JohnInTheGarage/Moonlyte/circuit/focuser/focuser.kicad_pcb

## KiCad design advanced-alu/schematics/advanced-alu/comparison-test-unit.kicad_sch

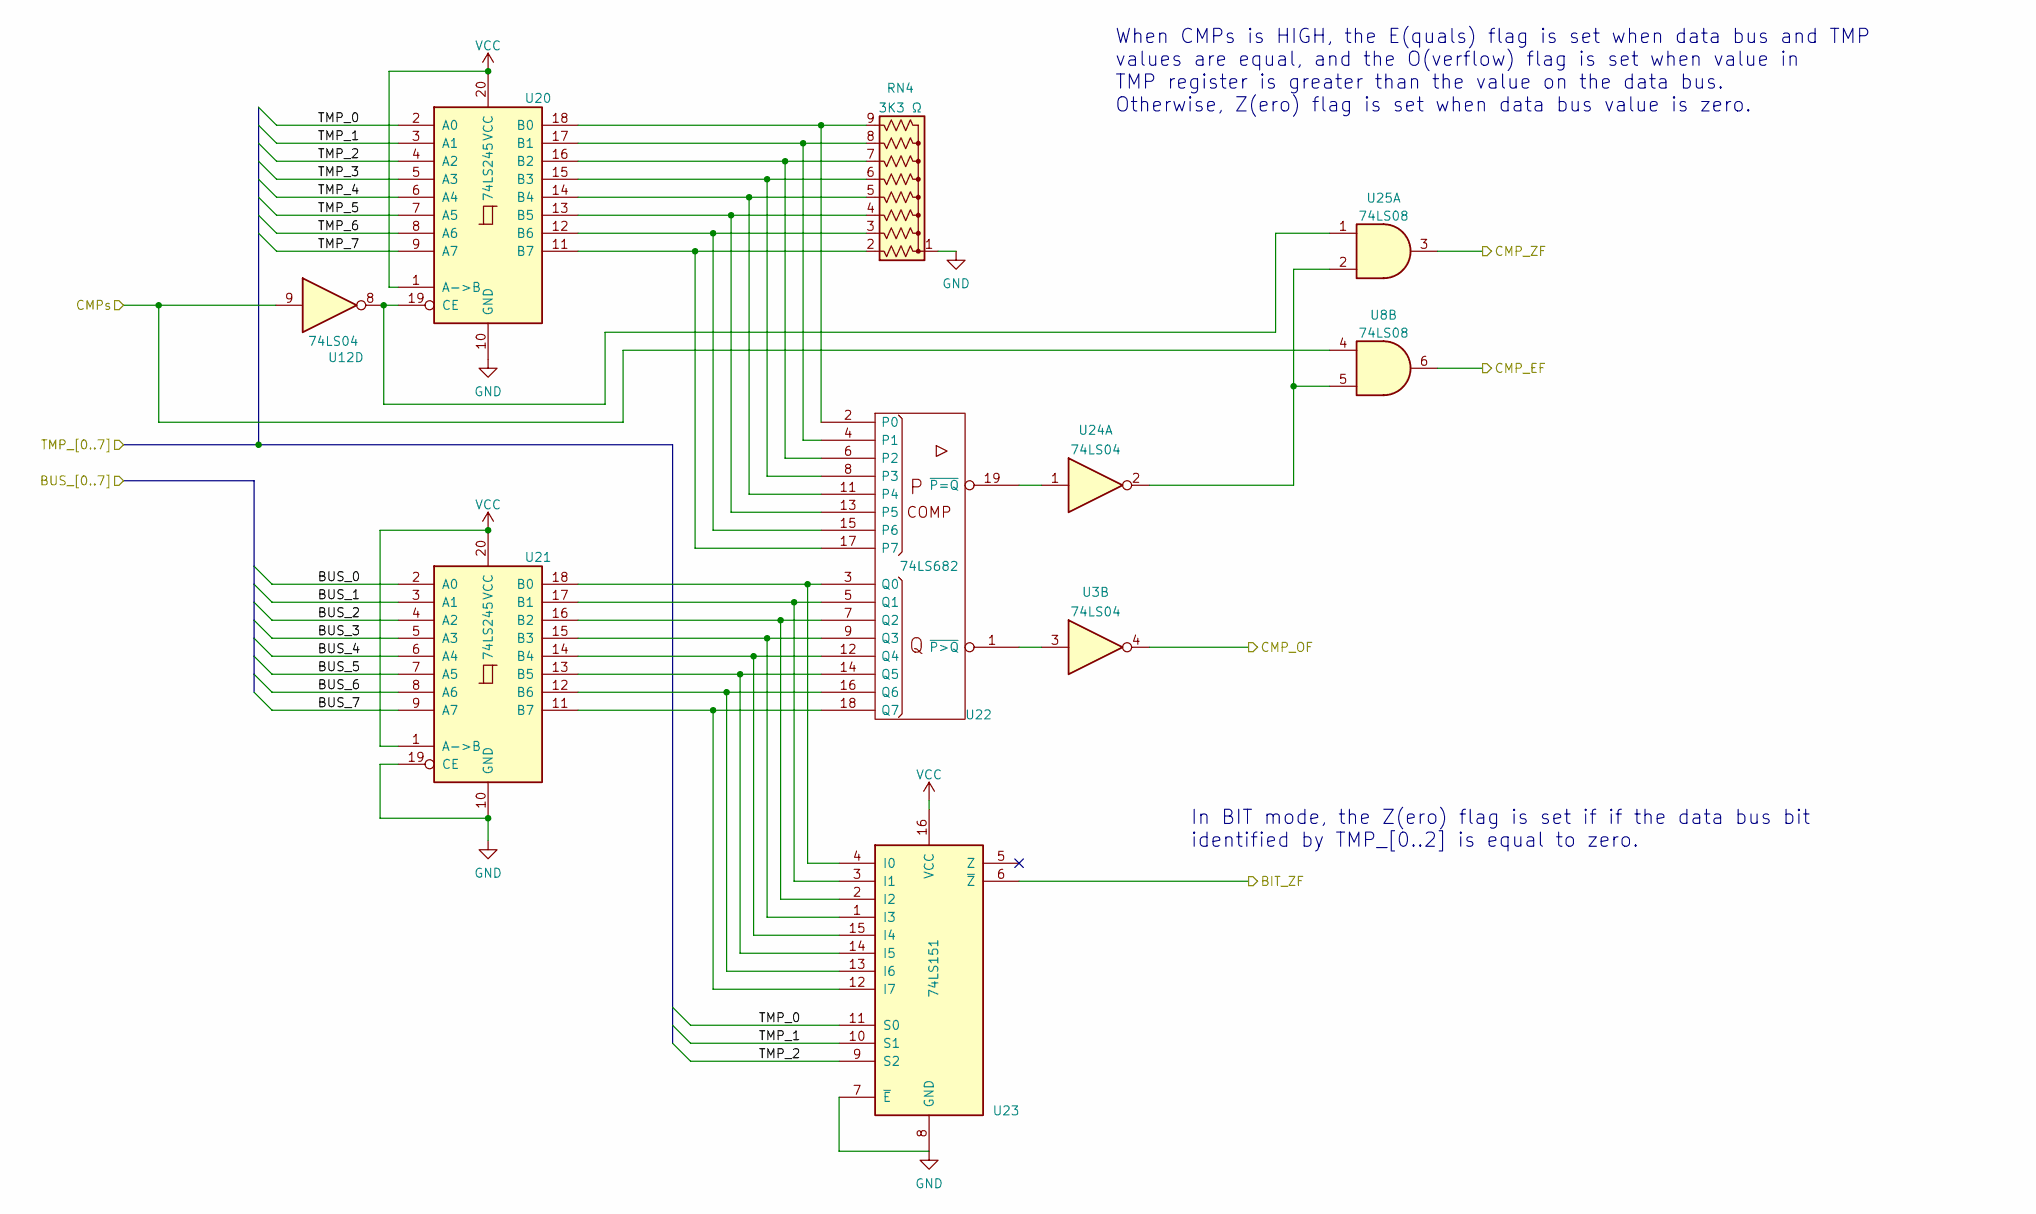
[picture p20: schematic comparison-test-unit.kicad_sch]

Parts:
RN4: 3K3 Ω; R_Array_SIP9
U3, U12, U24: 74LS04
U8, U25: 74LS08
U20, U21: 74LS245
U22: 74LS682
U23: 74LS151

Connections:
BIT_ZF: U23.6 (~Z)
BUS_0: U21.2 (A0)
BUS_1: U21.3 (A1)
BUS_2: U21.4 (A2)
BUS_3: U21.5 (A3)
BUS_4: U21.6 (A4)
BUS_5: U21.7 (A5)
BUS_6: U21.8 (A6)
BUS_7: U21.9 (A7)
CMP_EF: U8.6
CMP_OF: U3.4
CMP_ZF: U25.3
CMPs: U8.4, U12.9
GND: RN4.1 (common), U20.10 (GND), U21.10 (GND), U21.19 (CE), U23.7 (~E), U23.8 (GND)
unnamed: RN4.2 (R1), U20.11 (B7), U22.17 (P7)
unnamed: RN4.3 (R2), U20.12 (B6), U22.15 (P6)
unnamed: RN4.4 (R3), U20.13 (B5), U22.13 (P5)
unnamed: RN4.5 (R4), U20.14 (B4), U22.11 (P4)
unnamed: RN4.6 (R5), U20.15 (B3), U22.8 (P3)
unnamed: RN4.7 (R6), U20.16 (B2), U22.6 (P2)
unnamed: RN4.8 (R7), U20.17 (B1), U22.4 (P1)
unnamed: RN4.9 (R8), U20.18 (B0), U22.2 (P0)
unnamed: U12.8, U20.19 (CE), U25.1
unnamed: U21.11 (B7), U22.18 (Q7), U23.12 (I7)
unnamed: U21.12 (B6), U22.16 (Q6), U23.13 (I6)
unnamed: U21.13 (B5), U22.14 (Q5), U23.14 (I5)
unnamed: U21.14 (B4), U22.12 (Q4), U23.15 (I4)
unnamed: U21.15 (B3), U22.9 (Q3), U23.1 (I3)
unnamed: U21.16 (B2), U22.7 (Q2), U23.2 (I2)
unnamed: U21.17 (B1), U22.5 (Q1), U23.3 (I1)
unnamed: U21.18 (B0), U22.3 (Q0), U23.4 (I0)
unnamed: U3.3, U22.1 (~P>Q)
unnamed: U22.19 (~P=Q), U24.1
unnamed: U8.5, U24.2, U25.2
TMP_0: U20.2 (A0), U23.11 (S0)
TMP_1: U20.3 (A1), U23.10 (S1)
TMP_2: U20.4 (A2), U23.9 (S2)
TMP_3: U20.5 (A3)
TMP_4: U20.6 (A4)
TMP_5: U20.7 (A5)
TMP_6: U20.8 (A6)
TMP_7: U20.9 (A7)
VCC: U20.1 (A->B), U20.20 (VCC), U21.1 (A->B), U21.20 (VCC), U23.16 (VCC)

Notes on the sheet:
In BIT mode, the Z(ero) flag is set if if the data bus bit identified by TMP_[0..2] is equal to zero.
When CMPs is HIGH, the E(quals) flag is set when data bus and TMP values are equal, and the O(verflow) flag is set when value in TMP register is greater than the value on the data bus. Otherwise, Z(ero) flag is set when data bus value is zero.
