JohnInTheGarage/Moonlyte/circuit/focuser/focuser.kicad_pcb

## KiCad design advanced-alu/schematics/advanced-alu/flags-register.kicad_sch

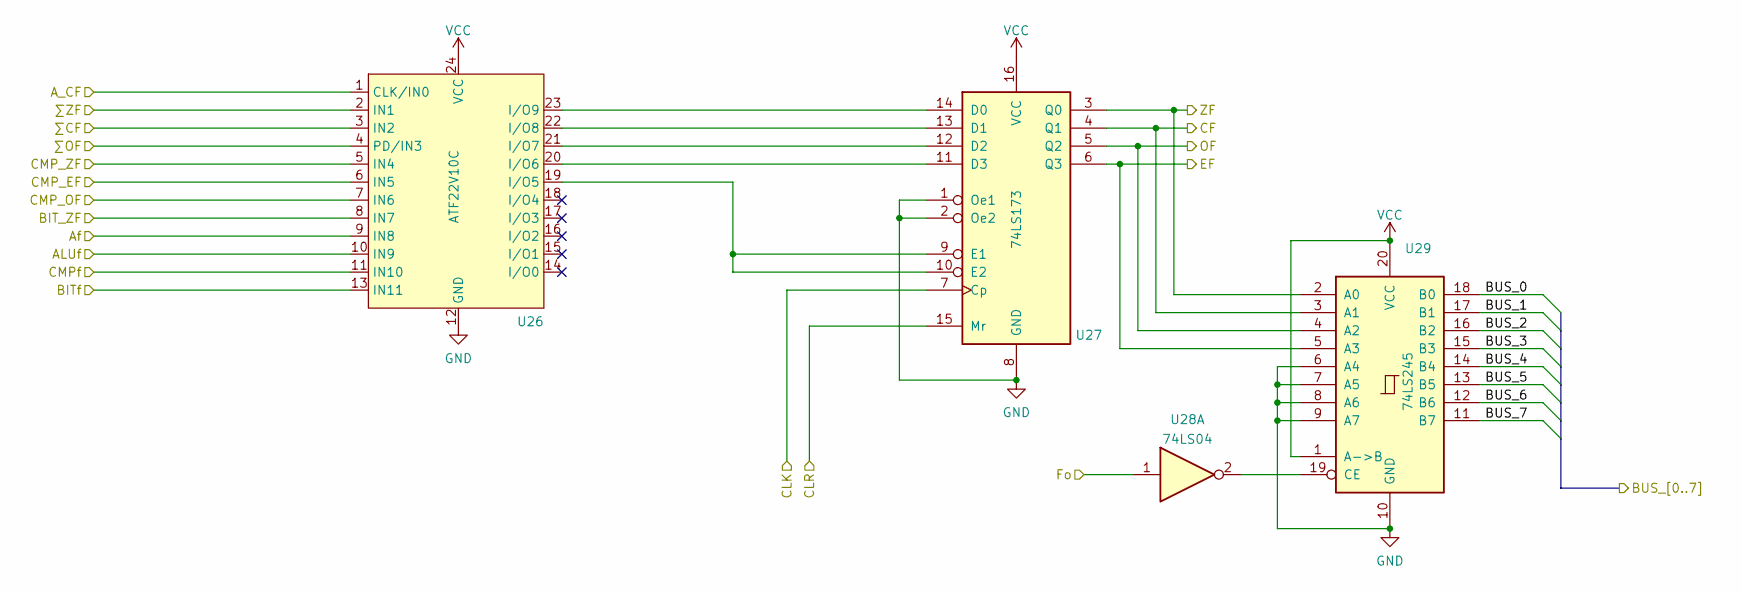
[picture p21: schematic flags-register.kicad_sch]

Parts:
U26: ATF22V10C
U27: 74LS173
U28: 74LS04
U29: 74LS245

Connections:
ALUf: U26.10 (IN9)
A_CF: U26.1 (CLK/IN0)
Af: U26.9 (IN8)
BIT_ZF: U26.8 (IN7)
BITf: U26.13 (IN11)
BUS_0: U29.18 (B0)
BUS_1: U29.17 (B1)
BUS_2: U29.16 (B2)
BUS_3: U29.15 (B3)
BUS_4: U29.14 (B4)
BUS_5: U29.13 (B5)
BUS_6: U29.12 (B6)
BUS_7: U29.11 (B7)
CF: U27.4 (Q1), U29.3 (A1)
CLK: U27.7 (Cp)
CLR: U27.15 (Mr)
CMP_EF: U26.6 (IN5)
CMP_OF: U26.7 (IN6)
CMP_ZF: U26.5 (IN4)
CMPf: U26.11 (IN10)
EF: U27.6 (Q3), U29.5 (A3)
Fo: U28.1
GND: U26.12 (GND), U27.1 (Oe1), U27.2 (Oe2), U27.8 (GND), U29.6 (A4), U29.7 (A5), U29.8 (A6), U29.9 (A7), U29.10 (GND)
unnamed: U26.19 (I/O5), U27.9 (E1), U27.10 (E2)
unnamed: U26.20 (I/O6), U27.11 (D3)
unnamed: U26.21 (I/O7), U27.12 (D2)
unnamed: U26.22 (I/O8), U27.13 (D1)
unnamed: U26.23 (I/O9), U27.14 (D0)
unnamed: U28.2, U29.19 (CE)
OF: U27.5 (Q2), U29.4 (A2)
VCC: U26.24 (VCC), U27.16 (VCC), U29.1 (A->B), U29.20 (VCC)
ZF: U27.3 (Q0), U29.2 (A0)
∑CF: U26.3 (IN2)
∑OF: U26.4 (PD/IN3)
∑ZF: U26.2 (IN1)
