JohnInTheGarage/Moonlyte/circuit/focuser/focuser.kicad_pcb

## KiCad design advanced-alu/schematics/control-logic/control-logic.kicad_sch

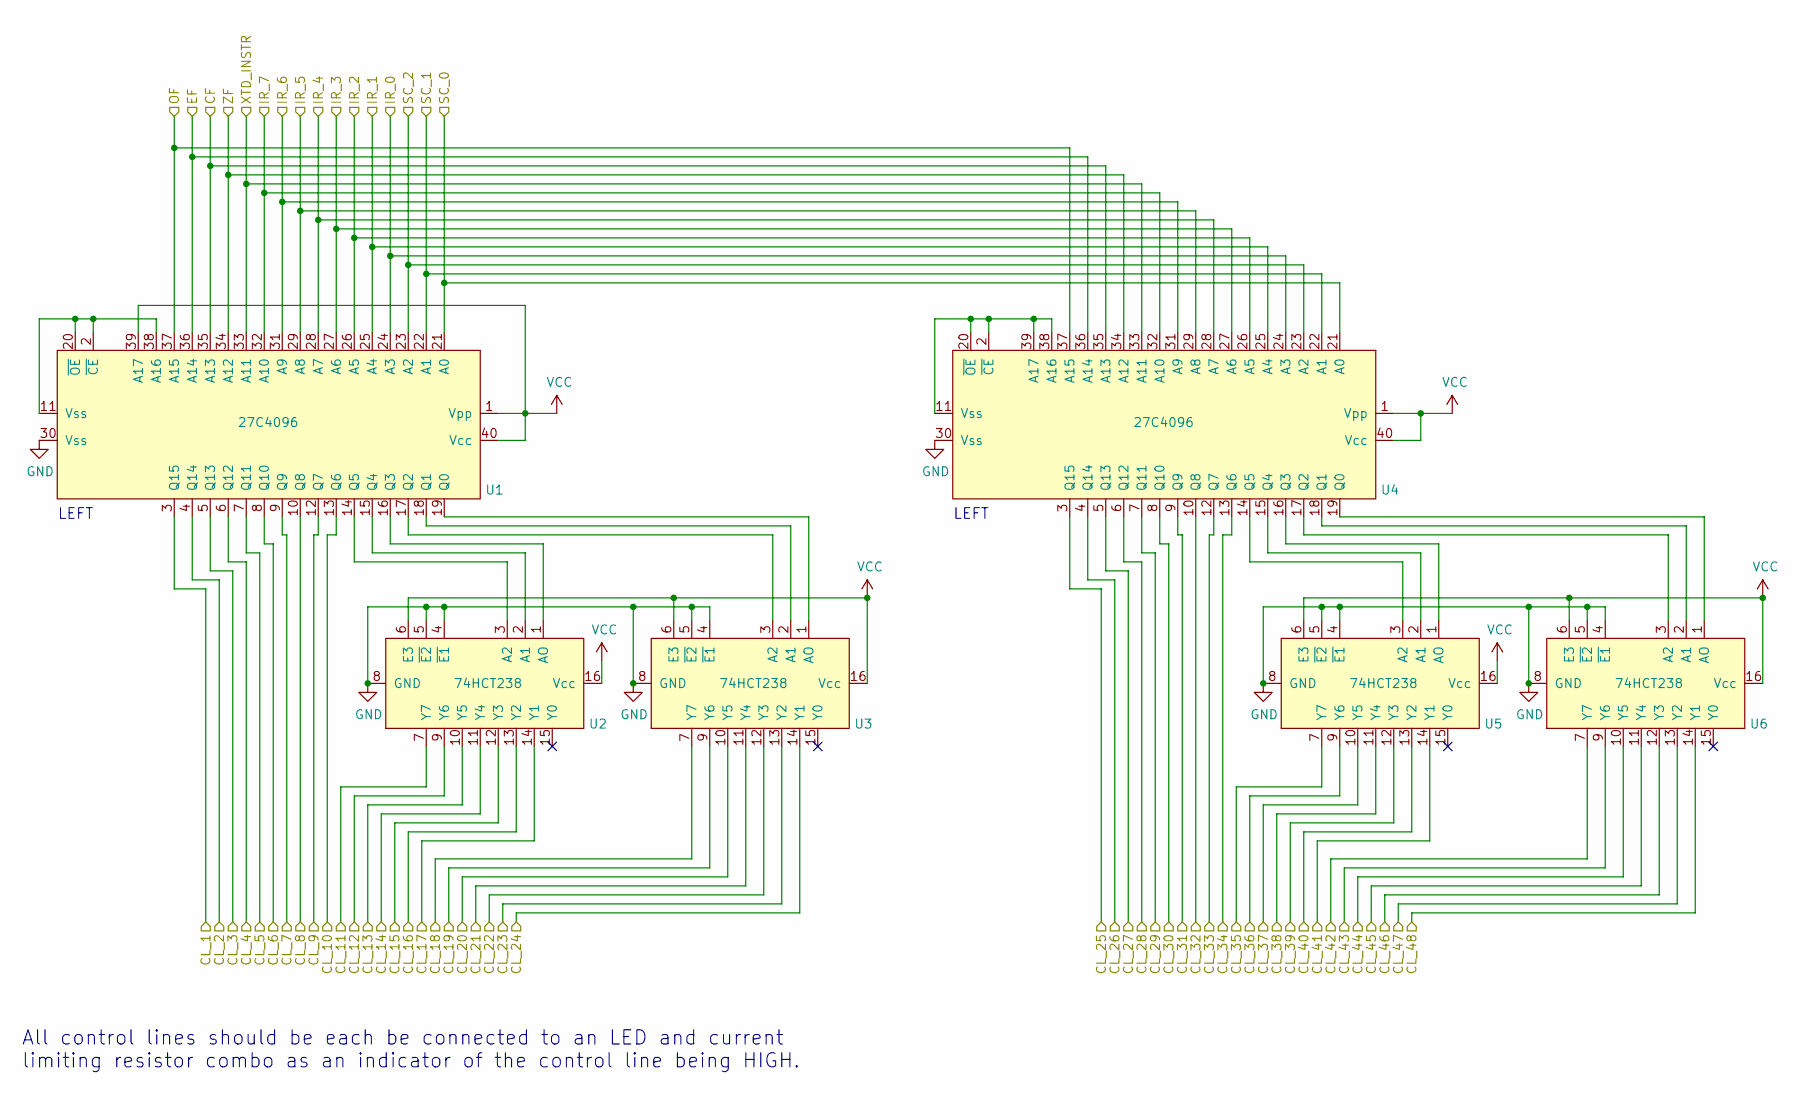
[picture p23: schematic control-logic.kicad_sch]

Parts:
U1, U4: 27C4096
U2, U3, U5, U6: 74HCT238

Connections:
CF: U1.35 (A13), U4.35 (A13)
CL_1: U1.3 (Q15)
CL_2: U1.4 (Q14)
CL_3: U1.5 (Q13)
CL_4: U1.6 (Q12)
CL_5: U1.7 (Q11)
CL_6: U1.8 (Q10)
CL_7: U1.9 (Q9)
CL_8: U1.10 (Q8)
CL_9: U1.12 (Q7)
CL_10: U1.13 (Q6)
CL_11: U2.7 (Y7)
CL_12: U2.9 (Y6)
CL_13: U2.10 (Y5)
CL_14: U2.11 (Y4)
CL_15: U2.12 (Y3)
CL_16: U2.13 (Y2)
CL_17: U2.14 (Y1)
CL_18: U3.7 (Y7)
CL_19: U3.9 (Y6)
CL_20: U3.10 (Y5)
CL_21: U3.11 (Y4)
CL_22: U3.12 (Y3)
CL_23: U3.13 (Y2)
CL_24: U3.14 (Y1)
CL_25: U4.3 (Q15)
CL_26: U4.4 (Q14)
CL_27: U4.5 (Q13)
CL_28: U4.6 (Q12)
CL_29: U4.7 (Q11)
CL_30: U4.8 (Q10)
CL_31: U4.9 (Q9)
CL_32: U4.10 (Q8)
CL_33: U4.12 (Q7)
CL_34: U4.13 (Q6)
CL_35: U5.7 (Y7)
CL_36: U5.9 (Y6)
CL_37: U5.10 (Y5)
CL_38: U5.11 (Y4)
CL_39: U5.12 (Y3)
CL_40: U5.13 (Y2)
CL_41: U5.14 (Y1)
CL_42: U6.7 (Y7)
CL_43: U6.9 (Y6)
CL_44: U6.10 (Y5)
CL_45: U6.11 (Y4)
CL_46: U6.12 (Y3)
CL_47: U6.13 (Y2)
CL_48: U6.14 (Y1)
EF: U1.36 (A14), U4.36 (A14)
GND: U1.30 (Vss), U2.4 (~E1), U2.5 (~E2), U2.8 (GND), U3.4 (~E1), U3.5 (~E2), U3.8 (GND), U4.30 (Vss), U5.4 (~E1), U5.5 (~E2), U5.8 (GND), U6.4 (~E1), U6.5 (~E2), U6.8 (GND)
IR_0: U1.24 (A3), U4.24 (A3)
IR_1: U1.25 (A4), U4.25 (A4)
IR_2: U1.26 (A5), U4.26 (A5)
IR_3: U1.27 (A6), U4.27 (A6)
IR_4: U1.28 (A7), U4.28 (A7)
IR_5: U1.29 (A8), U4.29 (A8)
IR_6: U1.31 (A9), U4.31 (A9)
IR_7: U1.32 (A10), U4.32 (A10)
unnamed: U1.2 (~CE), U1.11 (Vss), U1.20 (~OE), U1.38 (A16)
unnamed: U1.14 (Q5), U2.3 (A2)
unnamed: U1.15 (Q4), U2.2 (A1)
unnamed: U1.16 (Q3), U2.1 (AO)
unnamed: U1.17 (Q2), U3.3 (A2)
unnamed: U1.18 (Q1), U3.2 (A1)
unnamed: U1.19 (Q0), U3.1 (AO)
unnamed: U4.2 (~CE), U4.11 (Vss), U4.20 (~OE), U4.38 (A16), U4.39 (A17)
unnamed: U4.14 (Q5), U5.3 (A2)
unnamed: U4.15 (Q4), U5.2 (A1)
unnamed: U4.16 (Q3), U5.1 (AO)
unnamed: U4.17 (Q2), U6.3 (A2)
unnamed: U4.18 (Q1), U6.2 (A1)
unnamed: U4.19 (Q0), U6.1 (AO)
OF: U1.37 (A15), U4.37 (A15)
SC_0: U1.21 (A0), U4.21 (A0)
SC_1: U1.22 (A1), U4.22 (A1)
SC_2: U1.23 (A2), U4.23 (A2)
VCC: U1.1 (Vpp), U1.39 (A17), U1.40 (Vcc), U2.6 (E3), U2.16 (Vcc), U3.6 (E3), U3.16 (Vcc), U4.1 (Vpp), U4.40 (Vcc), U5.6 (E3), U5.16 (Vcc), U6.6 (E3), U6.16 (Vcc)
XTD_INSTR: U1.33 (A11), U4.33 (A11)
ZF: U1.34 (A12), U4.34 (A12)

Notes on the sheet:
All control lines should be each be connected to an LED and current limiting resistor combo as an indicator of the control line being HIGH.
LEFT
