JohnInTheGarage/Moonlyte/circuit/focuser/focuser.kicad_pcb

## KiCad design increment-registers/schematics/alu/alu.sch

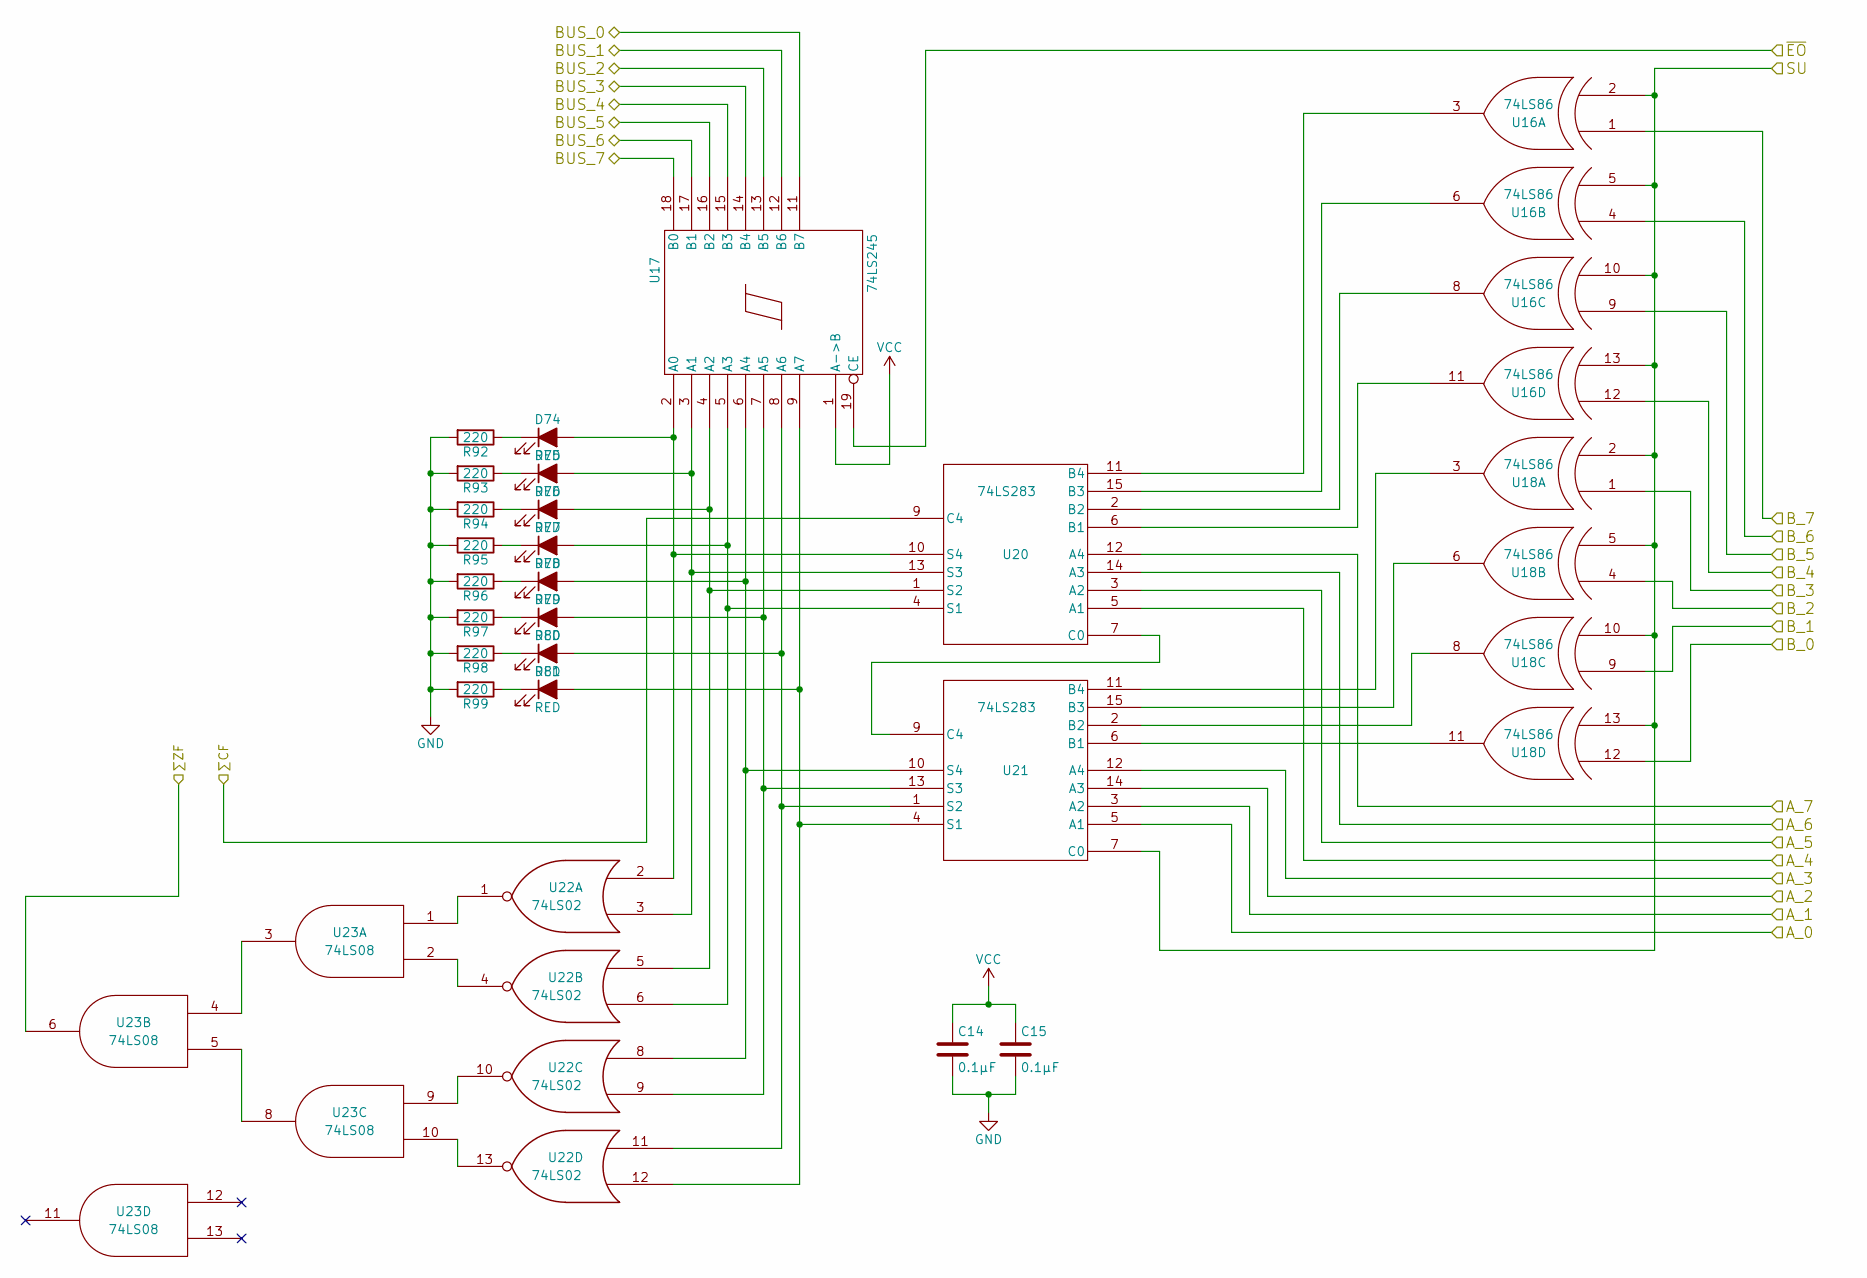
[picture p26: schematic alu.sch]

Parts:
C14, C15: 0.1µF; C_Disc_D4.3mm_W1.9mm_P5.00mm
D74, D75, D76, D77, D78, D79, D80, D81: RED; LED_D5.0mm
R92, R93, R94, R95, R96, R97, R98, R99: 220; R_Axial_DIN0207_L6.3mm_D2.5mm_P7.62mm_Horizontal
U16, U18: 74LS86; DIP-14_W7.62mm
U17: 74LS245; DIP-20_W7.62mm
U20, U21: 74LS283; DIP-16_W7.62mm
U22: 74LS02; DIP-14_W7.62mm
U23: 74LS08; DIP-14_W7.62mm

Connections:
A_0: U21.5 (A1)
A_1: U21.3 (A2)
A_2: U21.14 (A3)
A_3: U21.12 (A4)
A_4: U20.5 (A1)
A_5: U20.3 (A2)
A_6: U20.14 (A3)
A_7: U20.12 (A4)
BUS_0: U17.11 (B7)
BUS_1: U17.12 (B6)
BUS_2: U17.13 (B5)
BUS_3: U17.14 (B4)
BUS_4: U17.15 (B3)
BUS_5: U17.16 (B2)
BUS_6: U17.17 (B1)
BUS_7: U17.18 (B0)
B_0: U18.12 (IN1)
B_1: U18.9 (IN1)
B_2: U18.4 (IN1)
B_3: U18.1 (IN1)
B_4: U16.12 (IN1)
B_5: U16.9 (IN1)
B_6: U16.4 (IN1)
B_7: U16.1 (IN1)
GND: C14.2, C15.2, R92.2, R93.2, R94.2, R95.2, R96.2, R97.2, R98.2, R99.2
unnamed: D74.1 (K), R92.1
unnamed: D74.2 (A), U17.2 (A0), U20.10 (S4), U22.2
unnamed: D75.1 (K), R93.1
unnamed: D75.2 (A), U17.3 (A1), U20.13 (S3), U22.3
unnamed: D76.1 (K), R94.1
unnamed: D76.2 (A), U17.4 (A2), U20.1 (S2), U22.5
unnamed: D77.1 (K), R95.1
unnamed: D77.2 (A), U17.5 (A3), U20.4 (S1), U22.6
unnamed: D78.1 (K), R96.1
unnamed: D78.2 (A), U17.6 (A4), U21.10 (S4), U22.8
unnamed: D79.1 (K), R97.1
unnamed: D79.2 (A), U17.7 (A5), U21.13 (S3), U22.9
unnamed: D80.1 (K), R98.1
unnamed: D80.2 (A), U17.8 (A6), U21.1 (S2), U22.11
unnamed: D81.1 (K), R99.1
unnamed: D81.2 (A), U17.9 (A7), U21.4 (S1), U22.12
unnamed: U16.3 (OUT), U20.11 (B4)
unnamed: U16.6 (OUT), U20.15 (B3)
unnamed: U16.8 (OUT), U20.2 (B2)
unnamed: U16.11 (OUT), U20.6 (B1)
unnamed: U18.3 (OUT), U21.11 (B4)
unnamed: U18.6 (OUT), U21.15 (B3)
unnamed: U18.8 (OUT), U21.2 (B2)
unnamed: U18.11 (OUT), U21.6 (B1)
unnamed: U20.7 (C0), U21.9 (C4)
unnamed: U22.1, U23.1
unnamed: U22.4, U23.2
unnamed: U22.10, U23.9
unnamed: U22.13, U23.10
unnamed: U23.3, U23.4
unnamed: U23.5, U23.8
SU: U16.2 (IN2), U16.5 (IN2), U16.10 (IN2), U16.13 (IN2), U18.2 (IN2), U18.5 (IN2), U18.10 (IN2), U18.13 (IN2), U21.7 (C0)
VCC: C14.1, C15.1, U17.1 (A->B)
~EO: U17.19 (CE)
∑CF: U20.9 (C4)
∑ZF: U23.6
