JohnInTheGarage/Moonlyte/circuit/focuser/focuser.kicad_pcb

## KiCad design increment-registers/schematics/counting-register/counting-register.kicad_sch

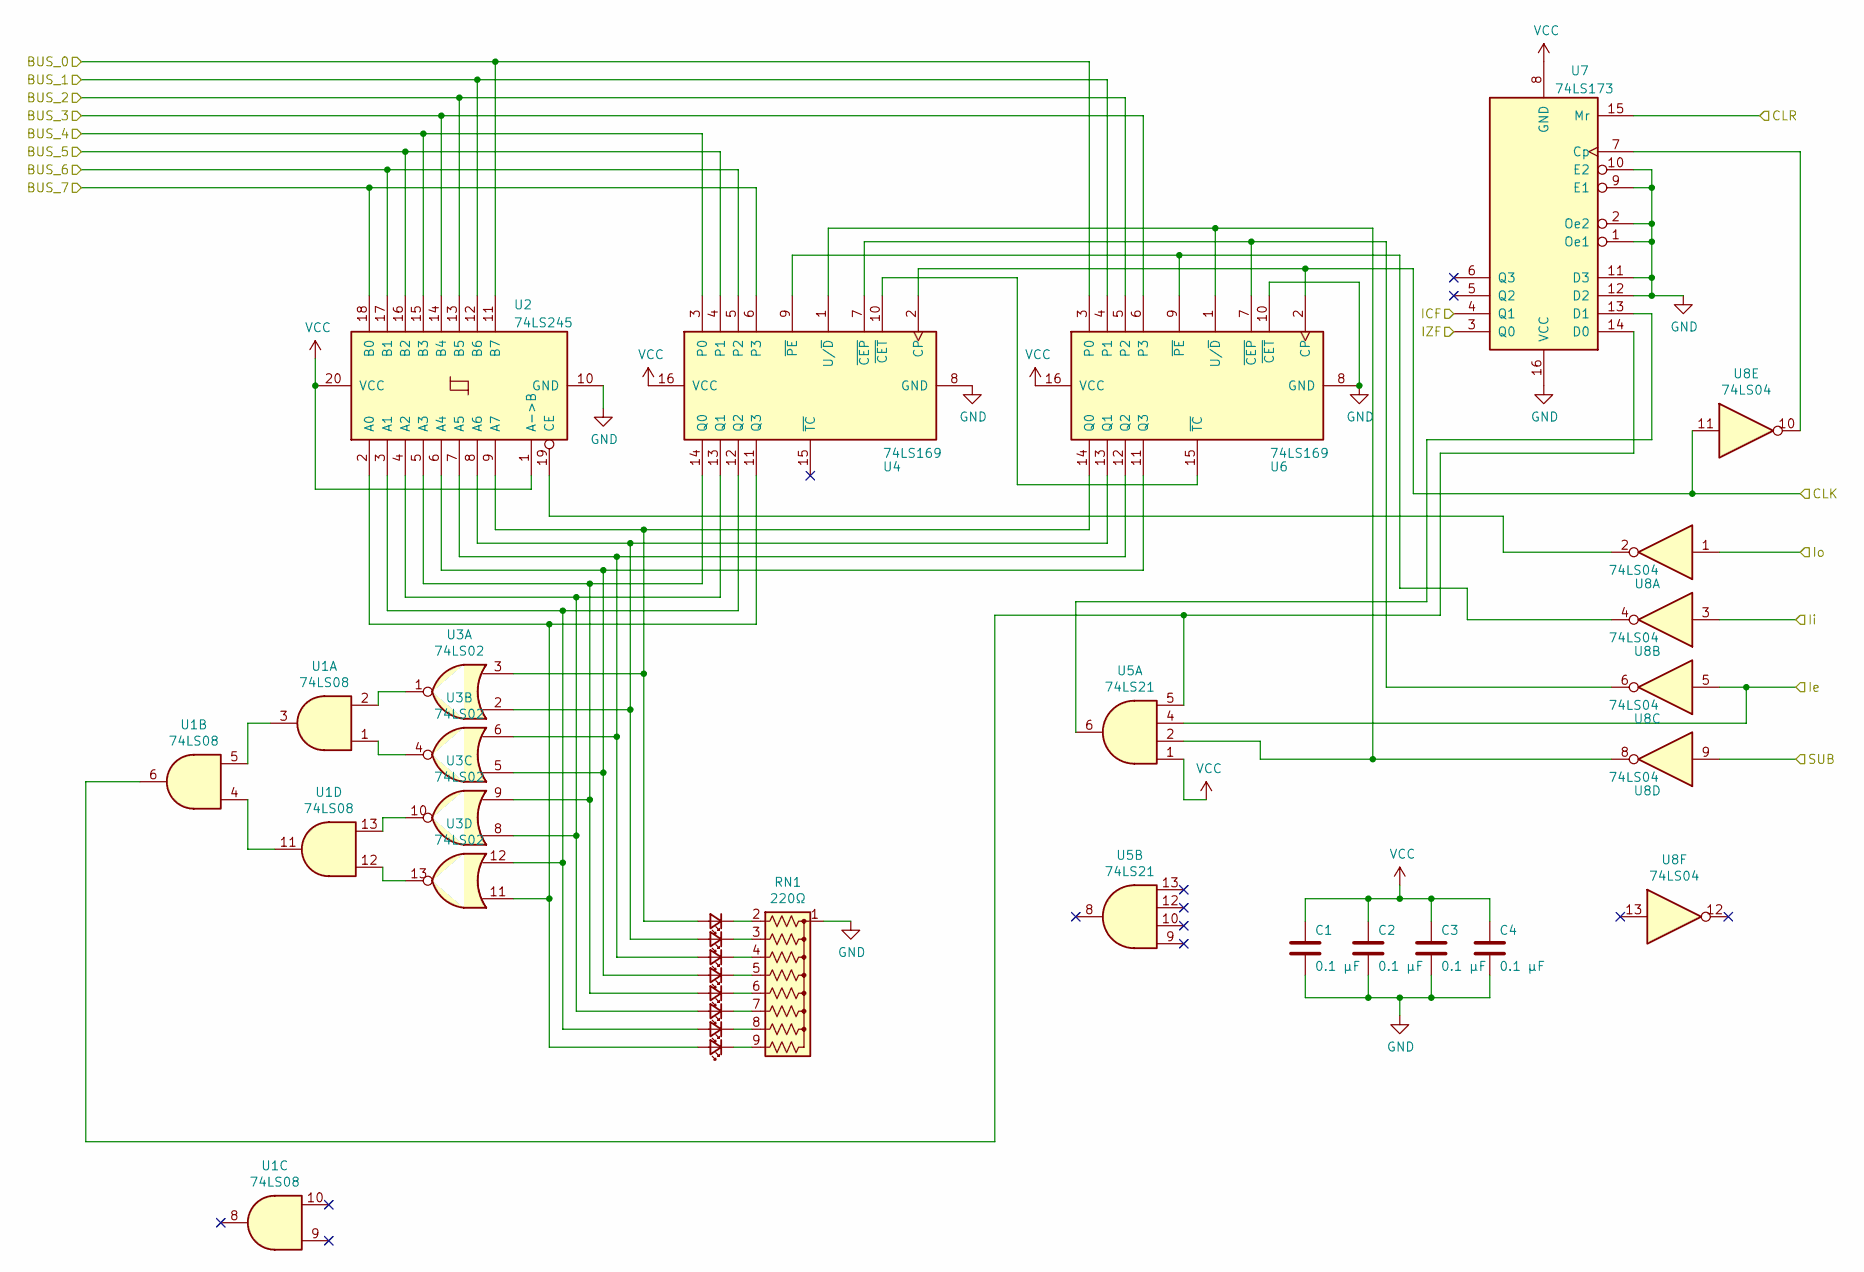
[picture p27: schematic counting-register.kicad_sch]

Parts:
C1, C2, C3, C4: 0.1 µF
D1, D2, D3, D4, D5, D6, D7, D8: LED_Small
RN1: 220Ω; R_Array_SIP9
U1: 74LS08
U2: 74LS245
U3: 74LS02
U4, U6: 74LS169
U5: 74LS21
U7: 74LS173
U8: 74LS04

Connections:
BUS_0: U2.11 (B7), U6.3 (P0)
BUS_1: U2.12 (B6), U6.4 (P1)
BUS_2: U2.13 (B5), U6.5 (P2)
BUS_3: U2.14 (B4), U6.6 (P3)
BUS_4: U2.15 (B3), U4.3 (P0)
BUS_5: U2.16 (B2), U4.4 (P1)
BUS_6: U2.17 (B1), U4.5 (P2)
BUS_7: U2.18 (B0), U4.6 (P3)
CLK: U4.2 (CP), U6.2 (CP), U8.11
CLR: U7.15 (Mr)
GND: C1.2, C2.2, C3.2, C4.2, RN1.1 (common), U2.10 (GND), U4.8 (GND), U6.8 (GND), U6.10 (~CET), U7.1 (Oe1), U7.2 (Oe2), U7.9 (E1), U7.10 (E2), U7.11 (D3), U7.12 (D2), U7.16 (VCC)
ICF: U7.4 (Q1)
IZF: U7.3 (Q0)
Ie: U5.4, U8.5
Ii: U8.3
Io: U8.1
unnamed: D1.1 (K), RN1.2 (R1)
unnamed: D1.2 (A), U2.9 (A7), U3.3, U6.14 (Q0)
unnamed: D2.1 (K), RN1.3 (R2)
unnamed: D2.2 (A), U2.8 (A6), U3.2, U6.13 (Q1)
unnamed: D3.1 (K), RN1.4 (R3)
unnamed: D3.2 (A), U2.7 (A5), U3.6, U6.12 (Q2)
unnamed: D4.1 (K), RN1.5 (R4)
unnamed: D4.2 (A), U2.6 (A4), U3.5, U6.11 (Q3)
unnamed: D5.1 (K), RN1.6 (R5)
unnamed: D5.2 (A), U2.5 (A3), U3.9, U4.14 (Q0)
unnamed: D6.1 (K), RN1.7 (R6)
unnamed: D6.2 (A), U2.4 (A2), U3.8, U4.13 (Q1)
unnamed: D7.1 (K), RN1.8 (R7)
unnamed: D7.2 (A), U2.3 (A1), U3.12, U4.12 (Q2)
unnamed: D8.1 (K), RN1.9 (R8)
unnamed: D8.2 (A), U2.2 (A0), U3.11, U4.11 (Q3)
unnamed: U1.1, U3.4
unnamed: U1.2, U3.1
unnamed: U1.3, U1.5
unnamed: U1.6, U5.5, U7.14 (D0)
unnamed: U1.4, U1.11
unnamed: U1.12, U3.13
unnamed: U1.13, U3.10
unnamed: U2.19 (CE), U8.2
unnamed: U4.1 (U/~D), U5.2, U6.1 (U/~D), U8.8
unnamed: U4.7 (~CEP), U6.7 (~CEP), U8.6
unnamed: U4.9 (~PE), U6.9 (~PE), U8.4
unnamed: U4.10 (~CET), U6.15 (~TC)
unnamed: U5.6, U7.13 (D1)
unnamed: U7.7 (Cp), U8.10
SUB: U8.9
VCC: C1.1, C2.1, C3.1, C4.1, U2.1 (A->B), U2.20 (VCC), U4.16 (VCC), U5.1, U6.16 (VCC), U7.8 (GND)
