JohnInTheGarage/Moonlyte/circuit/focuser/focuser.kicad_pcb

## KiCad design lcd-display/schematics/lcd-display/lcd-display.kicad_sch

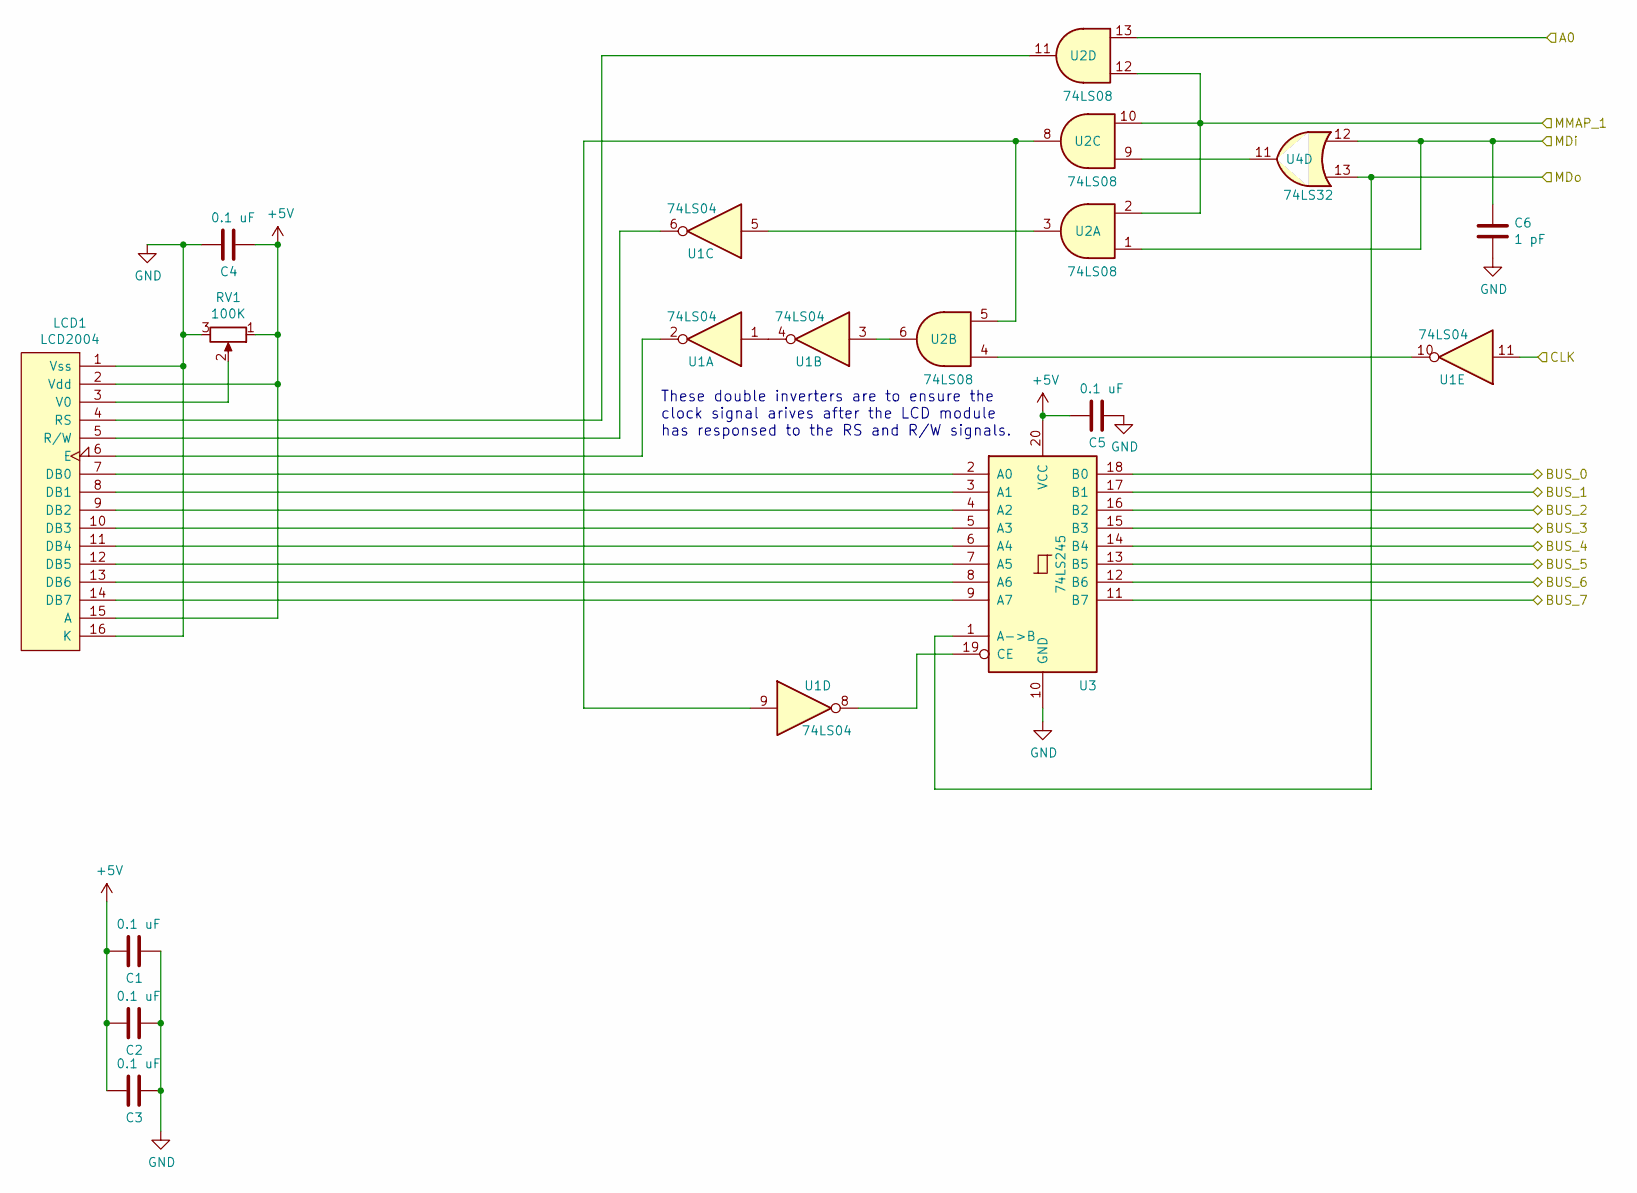
[picture p32: schematic lcd-display.kicad_sch]

Parts:
C1, C2, C3, C4, C5: 0.1 uF
C6: 1 pF
LCD1: LCD2004
RV1: 100K
U1: 74LS04
U2: 74LS08
U3: 74LS245
U4: 74LS32

Connections:
+5V: C1.2, C2.2, C3.2, C4.1, C5.2, LCD1.2 (Vdd), LCD1.15 (A), RV1.1, U3.20 (VCC)
A0: U2.13
BUS_0: U3.18 (B0)
BUS_1: U3.17 (B1)
BUS_2: U3.16 (B2)
BUS_3: U3.15 (B3)
BUS_4: U3.14 (B4)
BUS_5: U3.13 (B5)
BUS_6: U3.12 (B6)
BUS_7: U3.11 (B7)
CLK: U1.11
GND: C1.1, C2.1, C3.1, C4.2, C5.1, C6.2, LCD1.1 (Vss), LCD1.16 (K), RV1.3, U3.10 (GND)
MDi: C6.1, U2.1, U4.12
MDo: U3.1 (A->B), U4.13
MMAP_1: U2.2, U2.10, U2.12
unnamed: LCD1.3 (V0), RV1.2
unnamed: LCD1.4 (RS), U2.11
unnamed: LCD1.5 (R/W), U1.6
unnamed: LCD1.6 (E), U1.2
unnamed: LCD1.7 (DB0), U3.2 (A0)
unnamed: LCD1.8 (DB1), U3.3 (A1)
unnamed: LCD1.9 (DB2), U3.4 (A2)
unnamed: LCD1.10 (DB3), U3.5 (A3)
unnamed: LCD1.11 (DB4), U3.6 (A4)
unnamed: LCD1.12 (DB5), U3.7 (A5)
unnamed: LCD1.13 (DB6), U3.8 (A6)
unnamed: LCD1.14 (DB7), U3.9 (A7)
unnamed: U1.1, U1.4
unnamed: U1.3, U2.6
unnamed: U1.5, U2.3
unnamed: U1.8, U3.19 (CE)
unnamed: U1.9, U2.5, U2.8
unnamed: U1.10, U2.4
unnamed: U2.9, U4.11

Notes on the sheet:
These double inverters are to ensure the clock signal arives after the LCD module has responsed to the RS and R/W signals.
