JohnInTheGarage/Moonlyte/circuit/focuser/focuser.kicad_pcb

## KiCad design stack-pointer/schematics/index-register/index-register.kicad_sch

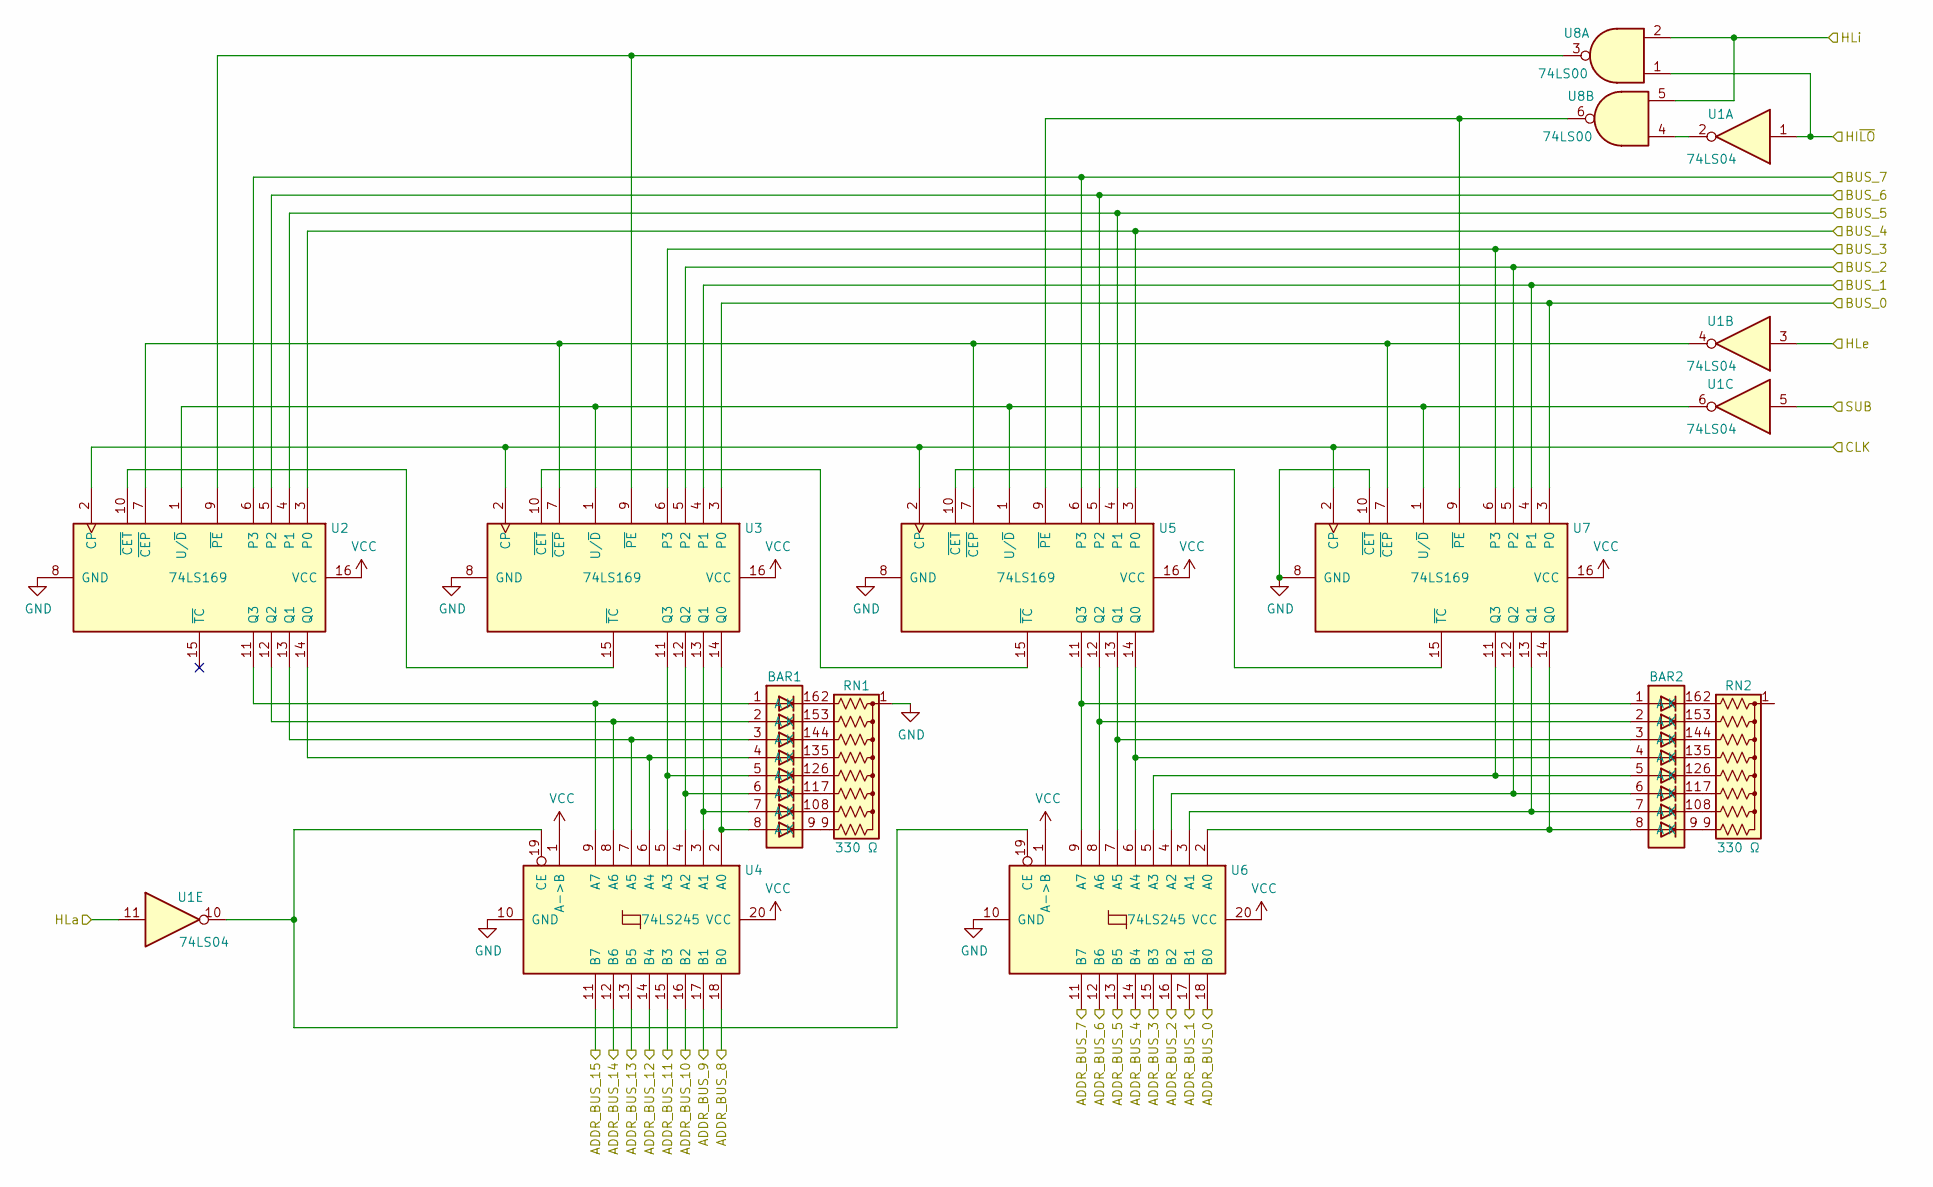
[picture p34: schematic index-register.kicad_sch]

Parts:
BAR1, BAR2: BarGraphLED_8P
RN1, RN2: 330 Ω; R_Array_SIP9
U1: 74LS04
U2, U3, U5, U7: 74LS169
U4, U6: 74LS245
U8: 74LS00

Connections:
ADDR_BUS_0: U6.18 (B0)
ADDR_BUS_1: U6.17 (B1)
ADDR_BUS_2: U6.16 (B2)
ADDR_BUS_3: U6.15 (B3)
ADDR_BUS_4: U6.14 (B4)
ADDR_BUS_5: U6.13 (B5)
ADDR_BUS_6: U6.12 (B6)
ADDR_BUS_7: U6.11 (B7)
ADDR_BUS_8: U4.18 (B0)
ADDR_BUS_9: U4.17 (B1)
ADDR_BUS_10: U4.16 (B2)
ADDR_BUS_11: U4.15 (B3)
ADDR_BUS_12: U4.14 (B4)
ADDR_BUS_13: U4.13 (B5)
ADDR_BUS_14: U4.12 (B6)
ADDR_BUS_15: U4.11 (B7)
BUS_0: U3.3 (P0), U7.3 (P0)
BUS_1: U3.4 (P1), U7.4 (P1)
BUS_2: U3.5 (P2), U7.5 (P2)
BUS_3: U3.6 (P3), U7.6 (P3)
BUS_4: U2.3 (P0), U5.3 (P0)
BUS_5: U2.4 (P1), U5.4 (P1)
BUS_6: U2.5 (P2), U5.5 (P2)
BUS_7: U2.6 (P3), U5.6 (P3)
CLK: U2.2 (CP), U3.2 (CP), U5.2 (CP), U7.2 (CP)
GND: RN1.1 (common), U2.8 (GND), U3.8 (GND), U4.10 (GND), U5.8 (GND), U6.10 (GND), U7.8 (GND), U7.10 (~CET)
HI~LO: U1.1, U8.1
HLa: U1.11
HLe: U1.3
HLi: U8.2, U8.5
unnamed: BAR1.1 (A), U2.11 (Q3), U4.9 (A7)
unnamed: BAR1.2 (A), U2.12 (Q2), U4.8 (A6)
unnamed: BAR1.3 (A), U2.13 (Q1), U4.7 (A5)
unnamed: BAR1.4 (A), U2.14 (Q0), U4.6 (A4)
unnamed: BAR1.5 (A), U3.11 (Q3), U4.5 (A3)
unnamed: BAR1.6 (A), U3.12 (Q2), U4.4 (A2)
unnamed: BAR1.7 (A), U3.13 (Q1), U4.3 (A1)
unnamed: BAR1.8 (A), U3.14 (Q0), U4.2 (A0)
unnamed: BAR1.9 (K), RN1.9 (R8)
unnamed: BAR1.10 (K), RN1.8 (R7)
unnamed: BAR1.11 (K), RN1.7 (R6)
unnamed: BAR1.12 (K), RN1.6 (R5)
unnamed: BAR1.13 (K), RN1.5 (R4)
unnamed: BAR1.14 (K), RN1.4 (R3)
unnamed: BAR1.15 (K), RN1.3 (R2)
unnamed: BAR1.16 (K), RN1.2 (R1)
unnamed: BAR2.1 (A), U5.11 (Q3), U6.9 (A7)
unnamed: BAR2.2 (A), U5.12 (Q2), U6.8 (A6)
unnamed: BAR2.3 (A), U5.13 (Q1), U6.7 (A5)
unnamed: BAR2.4 (A), U5.14 (Q0), U6.6 (A4)
unnamed: BAR2.5 (A), U6.5 (A3), U7.11 (Q3)
unnamed: BAR2.6 (A), U6.4 (A2), U7.12 (Q2)
unnamed: BAR2.7 (A), U6.3 (A1), U7.13 (Q1)
unnamed: BAR2.8 (A), U6.2 (A0), U7.14 (Q0)
unnamed: BAR2.9 (K), RN2.9 (R8)
unnamed: BAR2.10 (K), RN2.8 (R7)
unnamed: BAR2.11 (K), RN2.7 (R6)
unnamed: BAR2.12 (K), RN2.6 (R5)
unnamed: BAR2.13 (K), RN2.5 (R4)
unnamed: BAR2.14 (K), RN2.4 (R3)
unnamed: BAR2.15 (K), RN2.3 (R2)
unnamed: BAR2.16 (K), RN2.2 (R1)
unnamed: U1.2, U8.4
unnamed: U1.4, U2.7 (~CEP), U3.7 (~CEP), U5.7 (~CEP), U7.7 (~CEP)
unnamed: U1.6, U2.1 (U/~D), U3.1 (U/~D), U5.1 (U/~D), U7.1 (U/~D)
unnamed: U1.10, U4.19 (CE), U6.19 (CE)
unnamed: U2.9 (~PE), U3.9 (~PE), U8.3
unnamed: U2.10 (~CET), U3.15 (~TC)
unnamed: U3.10 (~CET), U5.15 (~TC)
unnamed: U5.9 (~PE), U7.9 (~PE), U8.6
unnamed: U5.10 (~CET), U7.15 (~TC)
SUB: U1.5
VCC: U2.16 (VCC), U3.16 (VCC), U4.1 (A->B), U4.20 (VCC), U5.16 (VCC), U6.1 (A->B), U6.20 (VCC), U7.16 (VCC)
