JohnInTheGarage/Moonlyte/circuit/focuser/focuser.kicad_pcb

## KiCad design stack-pointer/schematics/run-mode-selector-16bit/run-mode-selector-16bit.sch

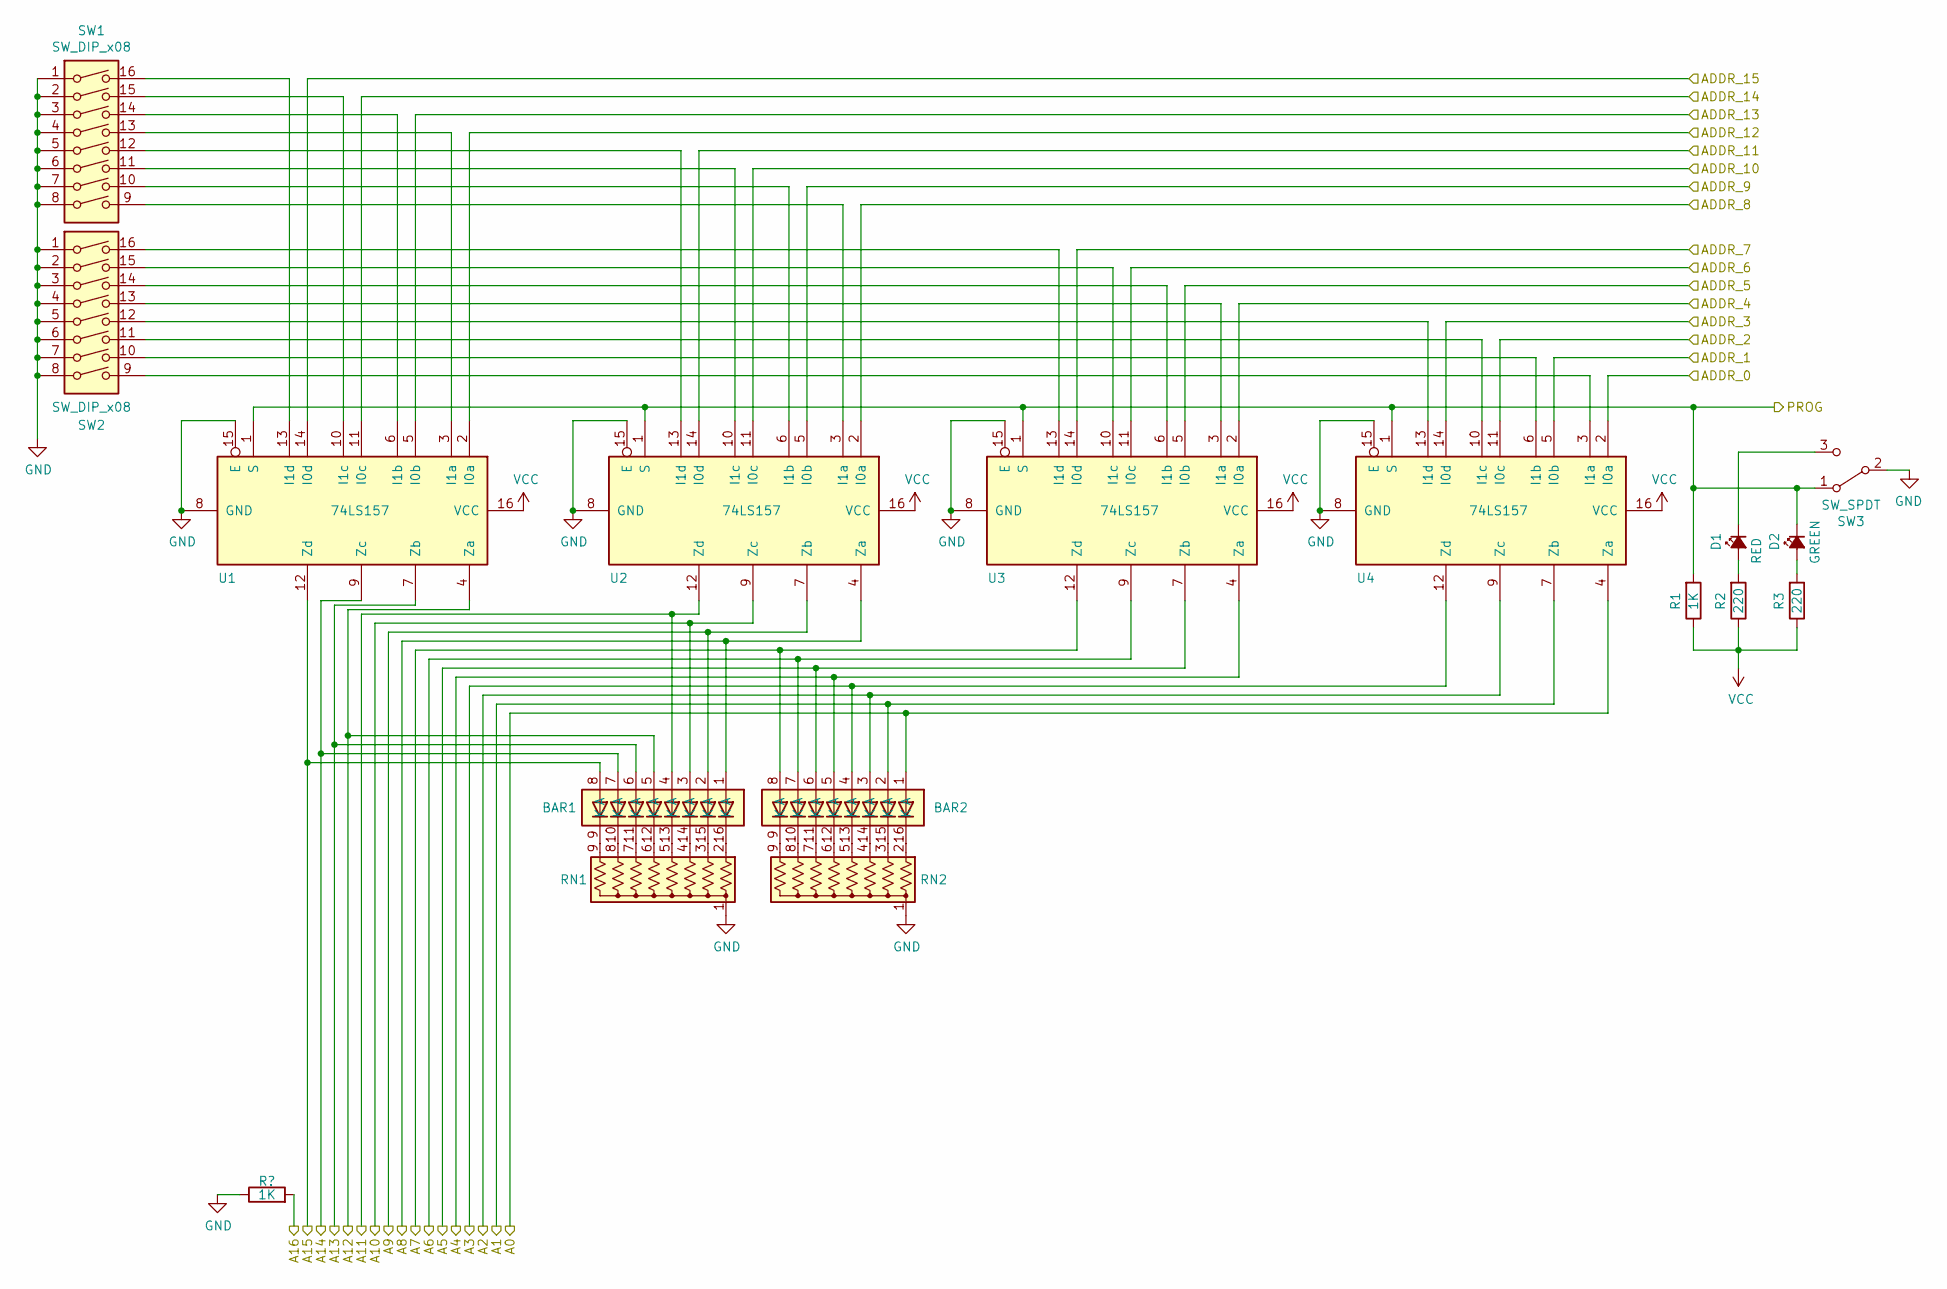
[picture p35: schematic run-mode-selector-16bit.sch]

Parts:
BAR1, BAR2: BarGraphLED_8P
D1: RED
D2: GREEN
R1: 1K
R2, R3: 220
RN1, RN2: R_Network08_US; R_Array_SIP9
SW1, SW2: SW_DIP_x08
SW3: SW_SPDT
U1, U2, U3, U4: 74LS157

Connections:
A0: BAR2.1 (A), U4.4 (Za)
A1: BAR2.2 (A), U4.7 (Zb)
A2: BAR2.3 (A), U4.9 (Zc)
A3: BAR2.4 (A), U4.12 (Zd)
A4: BAR2.5 (A), U3.4 (Za)
A5: BAR2.6 (A), U3.7 (Zb)
A6: BAR2.7 (A), U3.9 (Zc)
A7: BAR2.8 (A), U3.12 (Zd)
A8: BAR1.1 (A), U2.4 (Za)
A9: BAR1.2 (A), U2.7 (Zb)
A10: BAR1.3 (A), U2.9 (Zc)
A11: BAR1.4 (A), U2.12 (Zd)
A12: BAR1.5 (A), U1.4 (Za)
A13: BAR1.6 (A), U1.7 (Zb)
A14: BAR1.7 (A), U1.9 (Zc)
A15: BAR1.8 (A), U1.12 (Zd)
ADDR_0: U4.2 (I0a)
ADDR_1: U4.5 (I0b)
ADDR_2: U4.11 (I0c)
ADDR_3: U4.14 (I0d)
ADDR_4: U3.2 (I0a)
ADDR_5: U3.5 (I0b)
ADDR_6: U3.11 (I0c)
ADDR_7: U3.14 (I0d)
ADDR_8: U2.2 (I0a)
ADDR_9: U2.5 (I0b)
ADDR_10: U2.11 (I0c)
ADDR_11: U2.14 (I0d)
ADDR_12: U1.2 (I0a)
ADDR_13: U1.5 (I0b)
ADDR_14: U1.11 (I0c)
ADDR_15: U1.14 (I0d)
GND: RN1.1 (common), RN2.1 (common), SW1.1, SW1.2, SW1.3, SW1.4, SW1.5, SW1.6, SW1.7, SW1.8, SW2.1, SW2.2, SW2.3, SW2.4, SW2.5, SW2.6, SW2.7, SW2.8, SW3.2 (B), U1.8 (GND), U1.15 (E), U2.8 (GND), U2.15 (E), U3.8 (GND), U3.15 (E), U4.8 (GND), U4.15 (E)
unnamed: BAR1.9 (K), RN1.9 (R8)
unnamed: BAR1.10 (K), RN1.8 (R7)
unnamed: BAR1.11 (K), RN1.7 (R6)
unnamed: BAR1.12 (K), RN1.6 (R5)
unnamed: BAR1.13 (K), RN1.5 (R4)
unnamed: BAR1.14 (K), RN1.4 (R3)
unnamed: BAR1.15 (K), RN1.3 (R2)
unnamed: BAR1.16 (K), RN1.2 (R1)
unnamed: BAR2.9 (K), RN2.9 (R8)
unnamed: BAR2.10 (K), RN2.8 (R7)
unnamed: BAR2.11 (K), RN2.7 (R6)
unnamed: BAR2.12 (K), RN2.6 (R5)
unnamed: BAR2.13 (K), RN2.5 (R4)
unnamed: BAR2.14 (K), RN2.4 (R3)
unnamed: BAR2.15 (K), RN2.3 (R2)
unnamed: BAR2.16 (K), RN2.2 (R1)
unnamed: D1.1 (K), SW3.3 (C)
unnamed: D1.2 (A), R2.2
unnamed: D2.2 (A), R3.2
unnamed: SW1.9, U2.3 (I1a)
unnamed: SW1.10, U2.6 (I1b)
unnamed: SW1.11, U2.10 (I1c)
unnamed: SW1.12, U2.13 (I1d)
unnamed: SW1.13, U1.3 (I1a)
unnamed: SW1.14, U1.6 (I1b)
unnamed: SW1.15, U1.10 (I1c)
unnamed: SW1.16, U1.13 (I1d)
unnamed: SW2.9, U4.3 (I1a)
unnamed: SW2.10, U4.6 (I1b)
unnamed: SW2.11, U4.10 (I1c)
unnamed: SW2.12, U4.13 (I1d)
unnamed: SW2.13, U3.3 (I1a)
unnamed: SW2.14, U3.6 (I1b)
unnamed: SW2.15, U3.10 (I1c)
unnamed: SW2.16, U3.13 (I1d)
PROG: D2.1 (K), R1.2, SW3.1 (A), U1.1 (S), U2.1 (S), U3.1 (S), U4.1 (S)
VCC: R1.1, R2.1, R3.1, U1.16 (VCC), U2.16 (VCC), U3.16 (VCC), U4.16 (VCC)
