JohnInTheGarage/Moonlyte/circuit/focuser/focuser.kicad_pcb

## KiCad design stack-pointer/schematics/stack-pointer/stack-pointer.kicad_sch

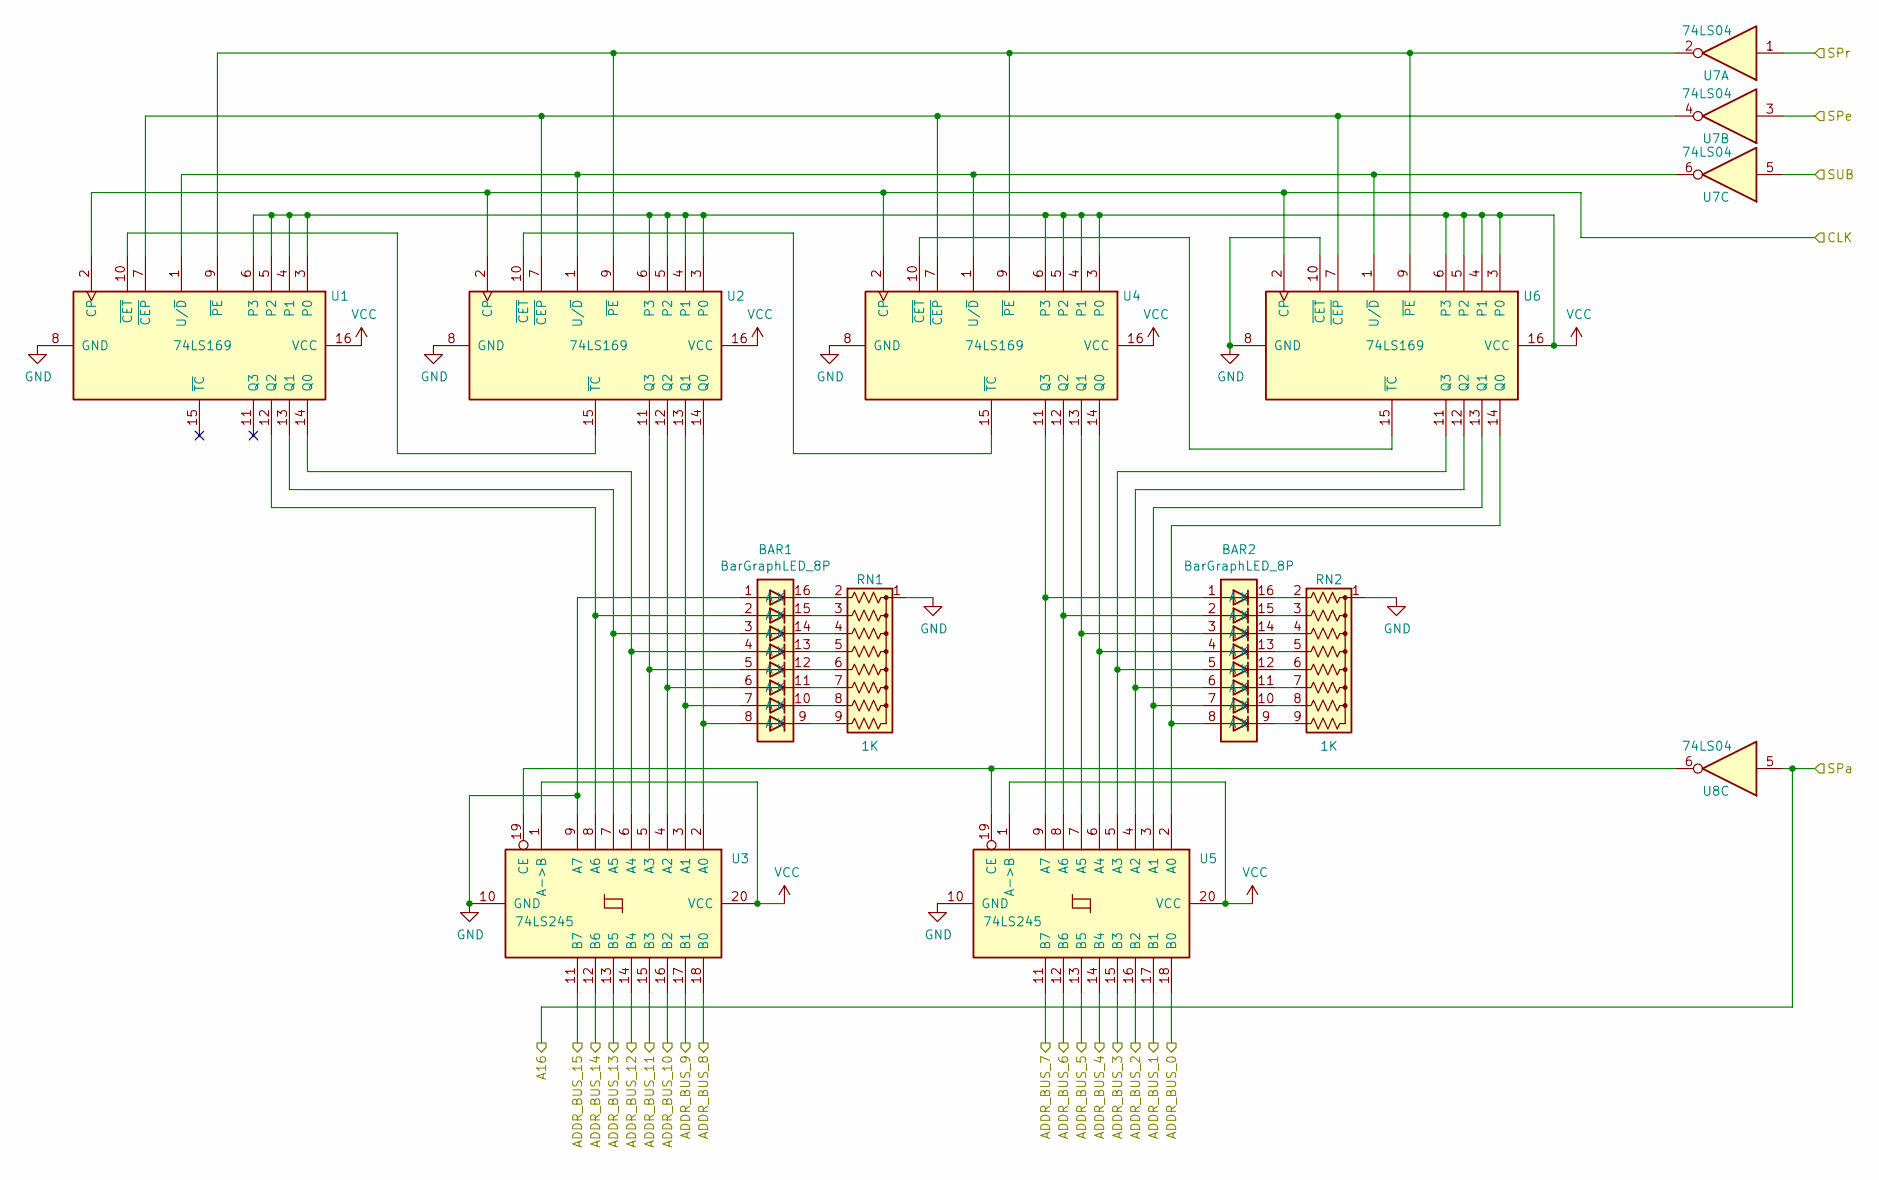
[picture p36: schematic stack-pointer.kicad_sch]

Parts:
BAR1, BAR2: BarGraphLED_8P
RN1, RN2: 1K; R_Array_SIP9
U1, U2, U4, U6: 74LS169
U3, U5: 74LS245
U7, U8: 74LS04

Connections:
A16: U8.5
ADDR_BUS_0: U5.18 (B0)
ADDR_BUS_1: U5.17 (B1)
ADDR_BUS_2: U5.16 (B2)
ADDR_BUS_3: U5.15 (B3)
ADDR_BUS_4: U5.14 (B4)
ADDR_BUS_5: U5.13 (B5)
ADDR_BUS_6: U5.12 (B6)
ADDR_BUS_7: U5.11 (B7)
ADDR_BUS_8: U3.18 (B0)
ADDR_BUS_9: U3.17 (B1)
ADDR_BUS_10: U3.16 (B2)
ADDR_BUS_11: U3.15 (B3)
ADDR_BUS_12: U3.14 (B4)
ADDR_BUS_13: U3.13 (B5)
ADDR_BUS_14: U3.12 (B6)
ADDR_BUS_15: U3.11 (B7)
CLK: U1.2 (CP), U2.2 (CP), U4.2 (CP), U6.2 (CP)
GND: BAR1.1 (A), RN1.1 (common), RN2.1 (common), U1.8 (GND), U2.8 (GND), U3.9 (A7), U3.10 (GND), U4.8 (GND), U5.10 (GND), U6.8 (GND), U6.10 (~CET)
unnamed: BAR1.2 (A), U1.12 (Q2), U3.8 (A6)
unnamed: BAR1.3 (A), U1.13 (Q1), U3.7 (A5)
unnamed: BAR1.4 (A), U1.14 (Q0), U3.6 (A4)
unnamed: BAR1.5 (A), U2.11 (Q3), U3.5 (A3)
unnamed: BAR1.6 (A), U2.12 (Q2), U3.4 (A2)
unnamed: BAR1.7 (A), U2.13 (Q1), U3.3 (A1)
unnamed: BAR1.8 (A), U2.14 (Q0), U3.2 (A0)
unnamed: BAR1.9 (K), RN1.9 (R8)
unnamed: BAR1.10 (K), RN1.8 (R7)
unnamed: BAR1.11 (K), RN1.7 (R6)
unnamed: BAR1.12 (K), RN1.6 (R5)
unnamed: BAR1.13 (K), RN1.5 (R4)
unnamed: BAR1.14 (K), RN1.4 (R3)
unnamed: BAR1.15 (K), RN1.3 (R2)
unnamed: BAR1.16 (K), RN1.2 (R1)
unnamed: BAR2.1 (A), U4.11 (Q3), U5.9 (A7)
unnamed: BAR2.2 (A), U4.12 (Q2), U5.8 (A6)
unnamed: BAR2.3 (A), U4.13 (Q1), U5.7 (A5)
unnamed: BAR2.4 (A), U4.14 (Q0), U5.6 (A4)
unnamed: BAR2.5 (A), U5.5 (A3), U6.11 (Q3)
unnamed: BAR2.6 (A), U5.4 (A2), U6.12 (Q2)
unnamed: BAR2.7 (A), U5.3 (A1), U6.13 (Q1)
unnamed: BAR2.8 (A), U5.2 (A0), U6.14 (Q0)
unnamed: BAR2.9 (K), RN2.9 (R8)
unnamed: BAR2.10 (K), RN2.8 (R7)
unnamed: BAR2.11 (K), RN2.7 (R6)
unnamed: BAR2.12 (K), RN2.6 (R5)
unnamed: BAR2.13 (K), RN2.5 (R4)
unnamed: BAR2.14 (K), RN2.4 (R3)
unnamed: BAR2.15 (K), RN2.3 (R2)
unnamed: BAR2.16 (K), RN2.2 (R1)
unnamed: U1.1 (U/~D), U2.1 (U/~D), U4.1 (U/~D), U6.1 (U/~D), U7.6
unnamed: U1.7 (~CEP), U2.7 (~CEP), U4.7 (~CEP), U6.7 (~CEP), U7.4
unnamed: U1.9 (~PE), U2.9 (~PE), U4.9 (~PE), U6.9 (~PE), U7.2
unnamed: U1.10 (~CET), U2.15 (~TC)
unnamed: U2.10 (~CET), U4.15 (~TC)
unnamed: U3.19 (CE), U5.19 (CE), U8.6
unnamed: U4.10 (~CET), U6.15 (~TC)
SPe: U7.3
SPr: U7.1
SUB: U7.5
VCC: U1.3 (P0), U1.4 (P1), U1.5 (P2), U1.6 (P3), U1.16 (VCC), U2.3 (P0), U2.4 (P1), U2.5 (P2), U2.6 (P3), U2.16 (VCC), U3.1 (A->B), U3.20 (VCC), U4.3 (P0), U4.4 (P1), U4.5 (P2), U4.6 (P3), U4.16 (VCC), U5.1 (A->B), U5.20 (VCC), U6.3 (P0), U6.4 (P1), U6.5 (P2), U6.6 (P3), U6.16 (VCC)
